sandrobenigno/WindRose/docs/images/wr_board.jpg

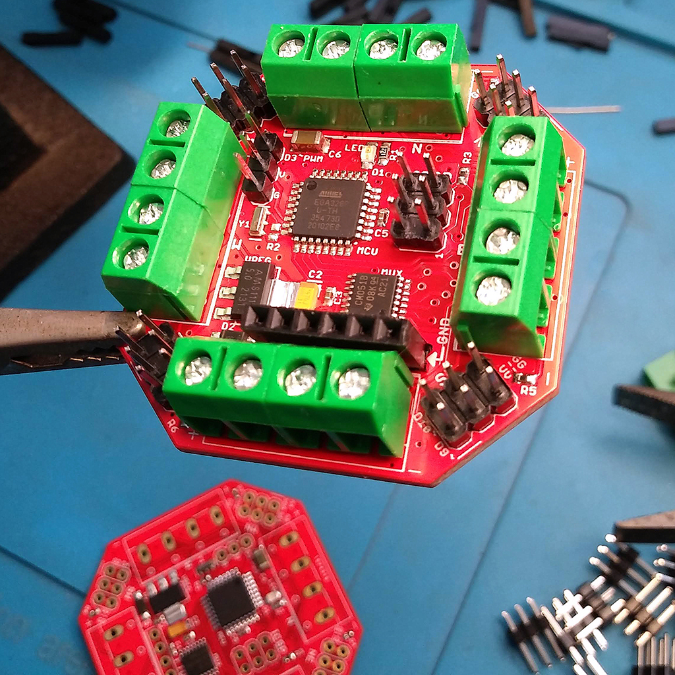
docs/images/wr_board.jpg
