sandrobenigno/WindRose/utilities/WindRoseMonitor/data/bg2.png

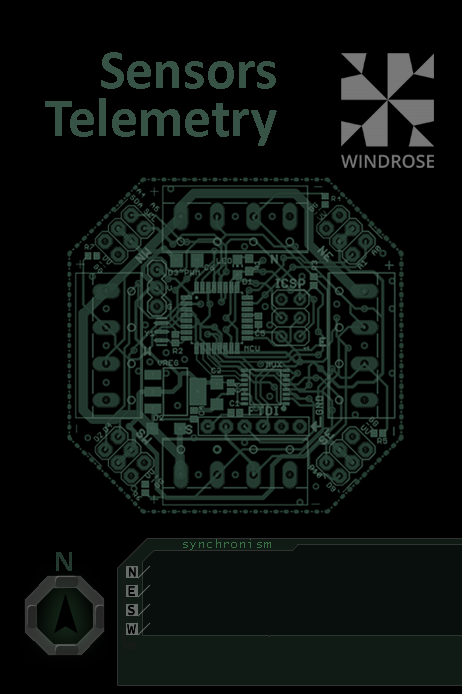
utilities/WindRoseMonitor/data/bg2.png
