sandrobenigno/WindRose/utilities/WindRoseMonitor/data/bg.png

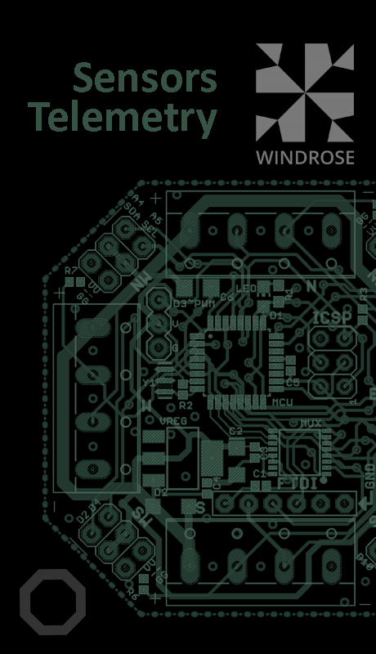
utilities/WindRoseMonitor/data/bg.png
