sandrobenigno/WindRose/src/WindRose.h

/** 
 * @file WindRose.h
 * @brief This file defines the WindRose's board class WRBoard (the body).
 * @author Sandro Benigno
 * @version 1.0
 * @date 2020-01-01
 */

#ifndef WindRose_h
#define WindRose_h

#include <Arduino.h>
#include "Directions.h"
#include "SSMachine.h" //Machine State for reading neighbours data
#include "WRMux.h" //WindRose Multiplexer class

/** @brief defines the LED pin */
#define WRLED A2 //redefine LED_BUILTIN to be the WR LED pin

/** @brief The class to control the LED 
 * @details The class LEDControl controls the WindRose's built-in LED. \n
 * We dont call it directly, instead we call it from the class WRBoard as <led>.
*/
class LEDControl {
  public:
    void on(){
        digitalWrite(WRLED, HIGH);
    }
    void off(){
        digitalWrite(WRLED, LOW);
    }
    void toggle(){
        digitalWrite(WRLED, !digitalRead(WRLED));
    }
};

/**
 * @brief The class to control the WindRose Board (the body).
 * @details The WindRose class holds the functions related directly to the board (the body). \n 
 * It controls the Multiplexer, the LEDs and runs the Serial State Machine.
*/
class WRBoard
{
    private:
    public:
        /** @brief The WindRose's Serial State Machine from the class SSMachine */
        SSMachine ssm; //Serial State Machine
        /** @brief The WindRose's Multiplexer Control from the class WRMux */
        WRMux mux; //Multiplexer controller
        /** @brief The WindRose's LED control from the class LEDControl */
        LEDControl led; //LED controller
        
        /** @brief Initializes the board by starting the LED, the Mux, the Serial Hardware, and the State Machine. */
        void init(uint16_t _baudrate){
            pinMode(WRLED, OUTPUT); //Set the LED pin as output
            this->led.on(); //Turn on the LED
            Serial.begin(_baudrate); //Start the Serial Hardware at specified baudrate
            this->ssm.setSerial(&Serial); //Set the serial port of the Serial State Machine
            this->mux.init(); //Set up the WindRose Mux
        }
};

#endif
