sandrobenigno/WindRose/src/Config.h

/**
 * @file Config.h
 * @brief This file is for keeping any general configuration parameters.
 * @author Sandro Benigno
 * @version 1.0
 * @date 2021-12-31
 */

#ifndef Config_h
#define Config_h
//#define WRDEBUG //Enables the debug mode when compiling
#define WRBAUDRATE 19200 //The baud rate of the serial port

#endif
