sandrobenigno/WindRose/utilities/WindRoseMonitor/WindRoseMonitor.pde

import processing.serial.*;
import controlP5.*;

ControlP5 cp5;
DropdownList serialPorts;
Button bt_StartStop;

Serial _stmRef;  // Create object from Serial class
int serial_port = 0;
final int BAUDRATE = 19200;
final int FPS = 25; 

//Drraw Control Variables
boolean ready = false;
int panelX = 30;
int panelY = 12;

SensingData_t sensdata;
String[] portNames;

/* ================================================== */

void setup() 
{
  size(1280, 700);
  frameRate(FPS);
  portNames = Serial.list();
  
  cp5 = new ControlP5(this);
  serialPorts = cp5.addDropdownList("Serial Port...").setPosition(1080,10);
  for(int i = 0 ; i < portNames.length; i++) serialPorts.addItem(portNames[i], i);
  customize(serialPorts);

  bt_StartStop = cp5.addButton("Start");
  customize(bt_StartStop, false);

  initImages();
  sensdata = new SensingData_t();
  println("Program started!");
}

void draw()
{
  if(ready){
    if(millis() - lastget > 100){ //Loop of data grabbing (10Hz)
      getData(); //Call the state machine
      lastget = millis();
    }
    if(pack_ok){
        drawBG();
        drawGrid();
        drawLPPS();
      if(millis() - lastlost > 15000){ //Loop of Lost Packs Calculation (4 p/ min)
        lostrate = lostpack * 4; //Four times the loss of 15sec = loss per minute
        lostpack = 0;
        lastlost = millis();
      }
      drawNGM();
      drawAge();
      drawSensors();
      println("NGM: "+binary(NGM)+" ASBM: "+binary(int(ASBM))+" Light.lux="+sensdata.light.lux);
    }
  }
  else{
    drawBG();
    drawGrid();
  }
}
